Nurgak/Internet-of-Things-Power-Meter/Pictures/Misc/2015-12-24 13.48.35.jpg

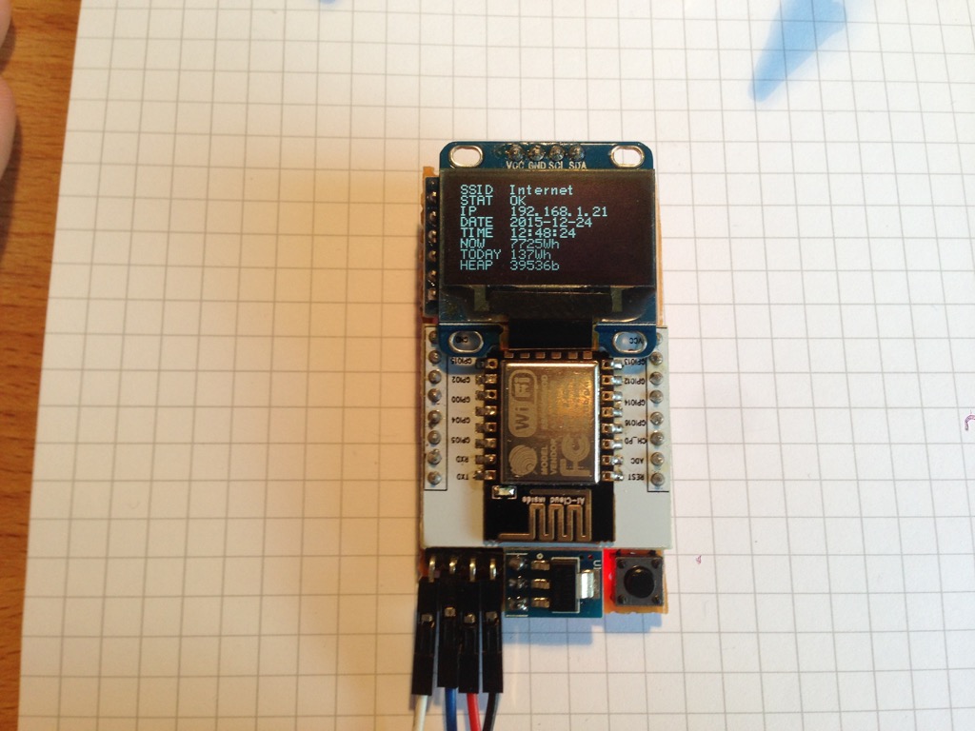
Pictures/Misc/2015-12-24 13.48.35.jpg
