Nurgak/Internet-of-Things-Power-Meter/Pictures/Misc/2015-12-24 13.49.23.jpg

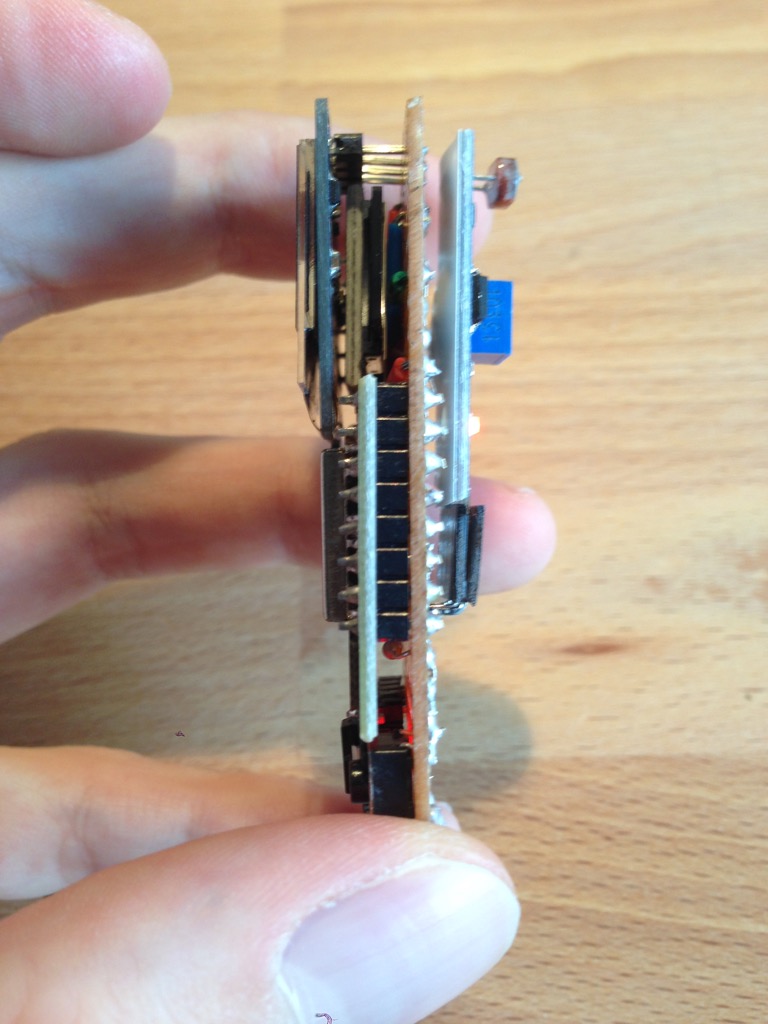
Pictures/Misc/2015-12-24 13.49.23.jpg
