Nurgak/Internet-of-Things-Power-Meter/Pictures/Misc/2015-12-24 13.50.25.jpg

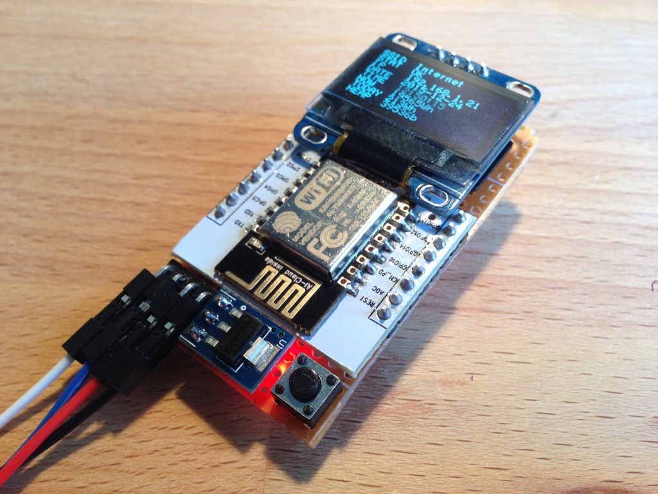
Pictures/Misc/2015-12-24 13.50.25.jpg
