Nurgak/Internet-of-Things-Power-Meter/Pictures/Misc/2016-03-25 19.55.58.jpg

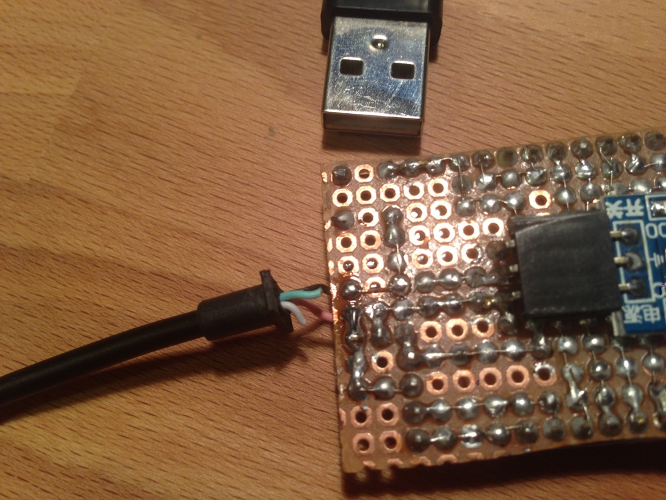
Pictures/Misc/2016-03-25 19.55.58.jpg
