Nurgak/Internet-of-Things-Power-Meter/Pictures/Misc/2016-03-27 12.49.37.jpg

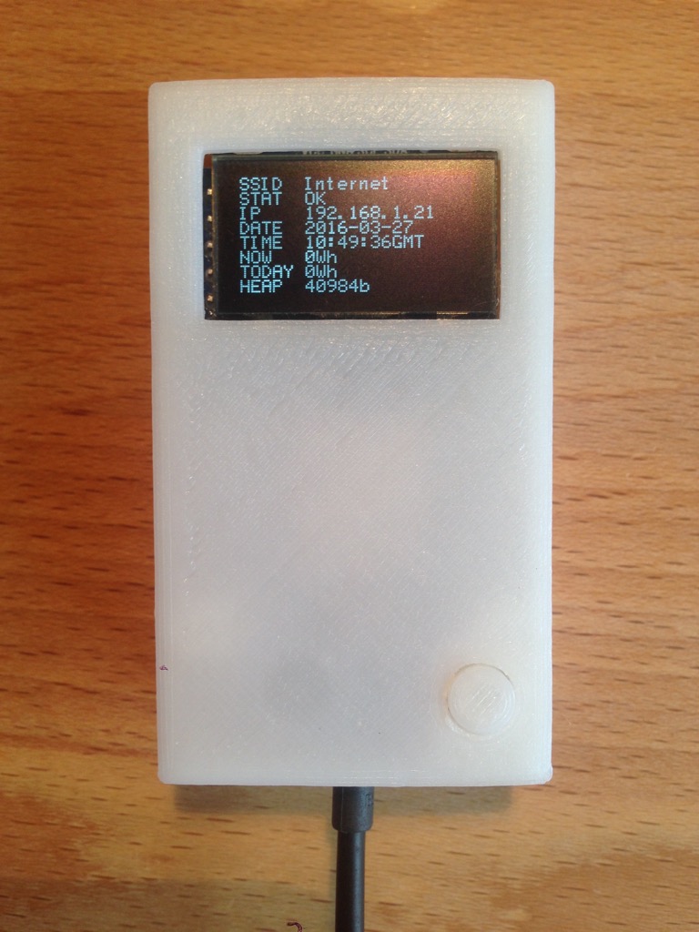
Pictures/Misc/2016-03-27 12.49.37.jpg
