Nurgak/Internet-of-Things-Power-Meter/Pictures/Misc/2016-03-27 12.50.36.jpg

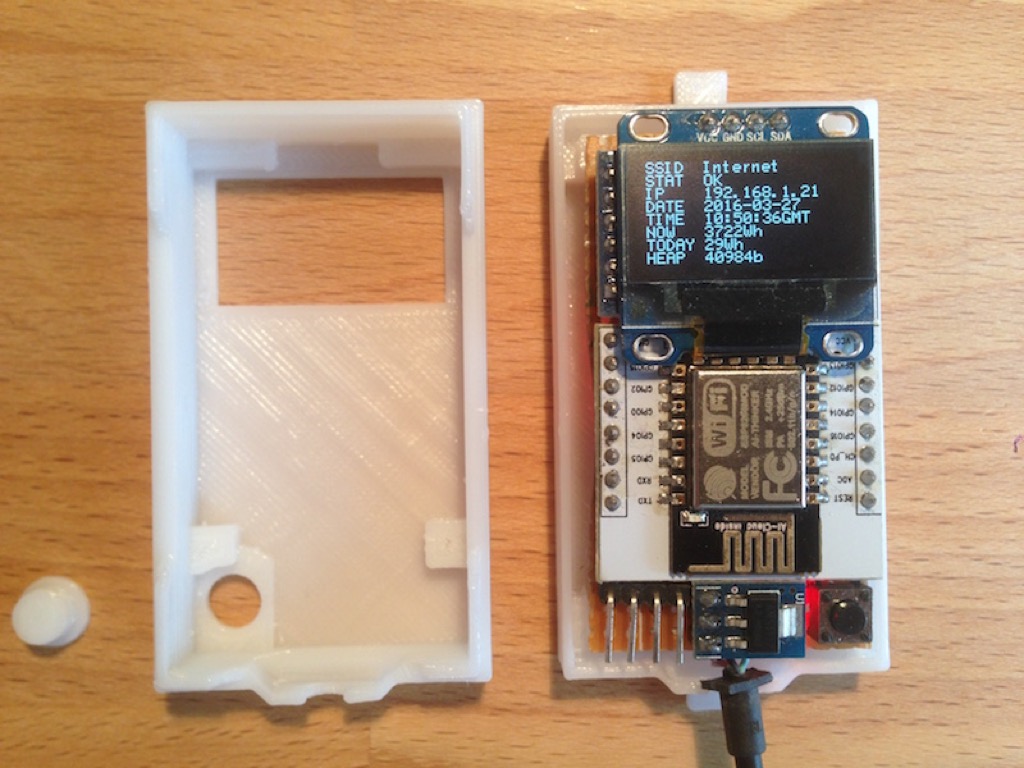
Pictures/Misc/2016-03-27 12.50.36.jpg
