Nurgak/Internet-of-Things-Power-Meter/Pictures/Misc/2016-03-27 13.48.42.jpg

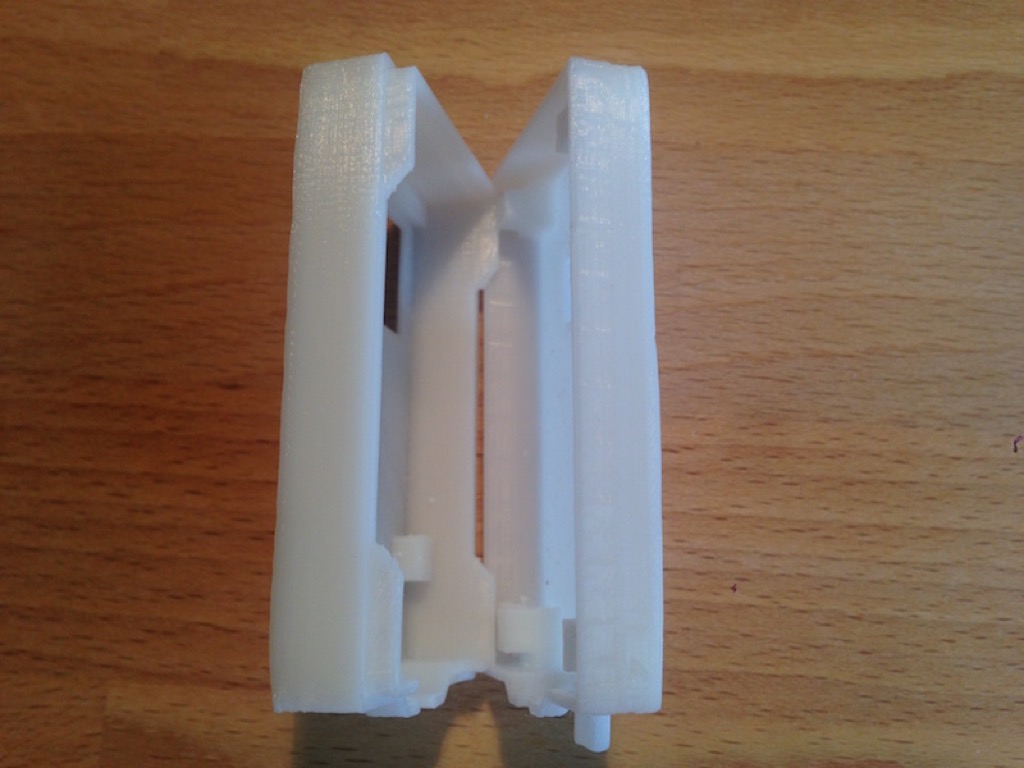
Pictures/Misc/2016-03-27 13.48.42.jpg
