Nurgak/Internet-of-Things-Power-Meter/Pictures/Misc/Graph.png

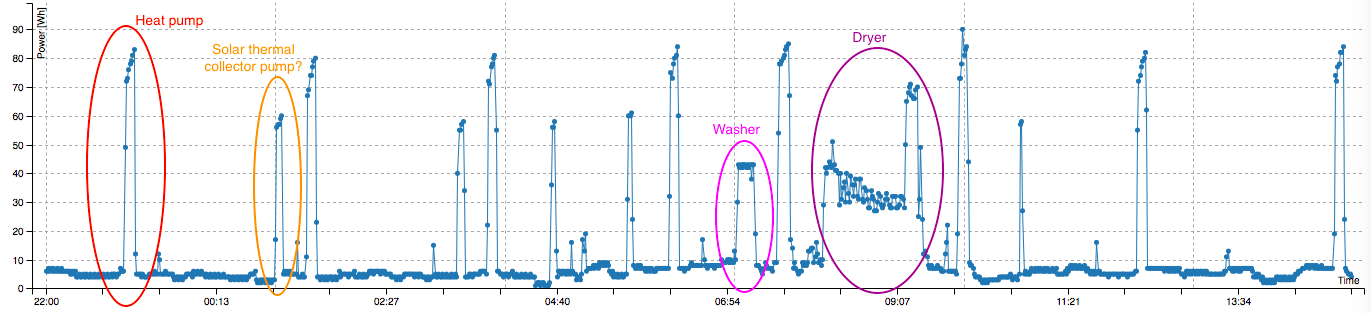
Pictures/Misc/Graph.png
