Nurgak/Internet-of-Things-Power-Meter/Pictures/Misc/IoT_Power_Meter_02.jpg

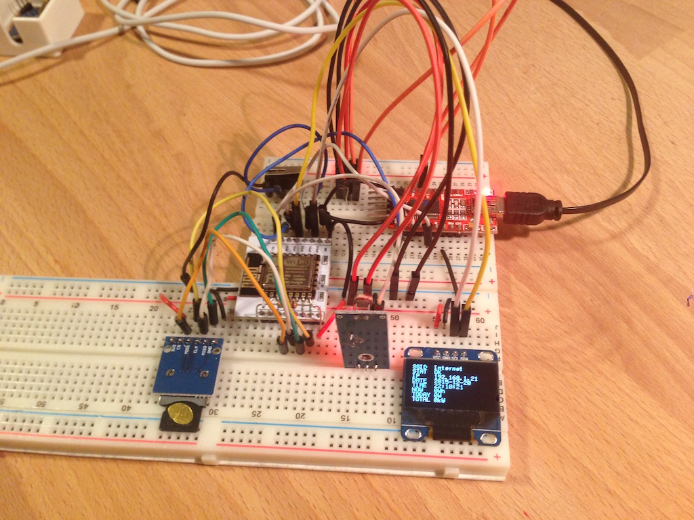
Pictures/Misc/IoT_Power_Meter_02.jpg
