Nurgak/Internet-of-Things-Power-Meter/Pictures/Misc/IPM.jpg

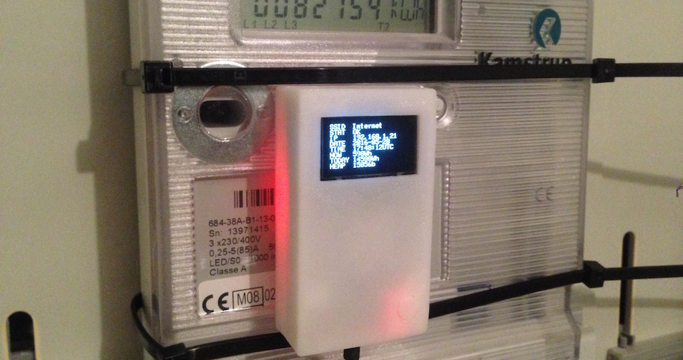
Pictures/Misc/IPM.jpg
