Nurgak/Internet-of-Things-Power-Meter/Pictures/Build/2015-12-22 19.23.27.jpg

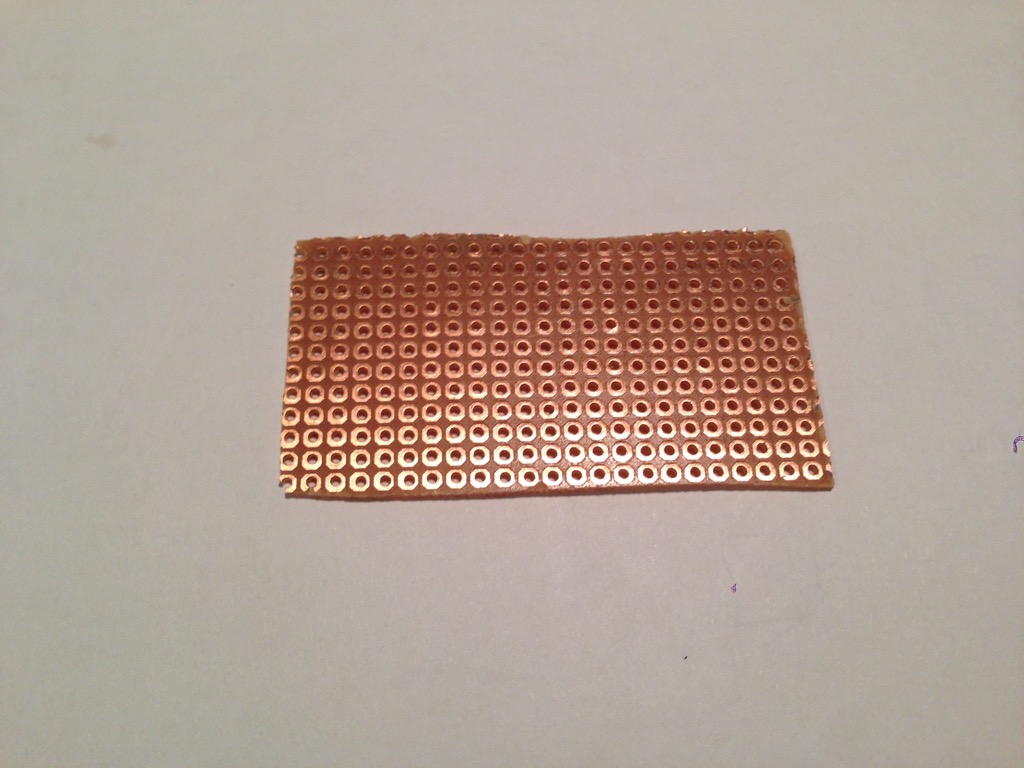
Pictures/Build/2015-12-22 19.23.27.jpg
