Nurgak/Internet-of-Things-Power-Meter/Pictures/Build/2015-12-23 22.53.20.jpg

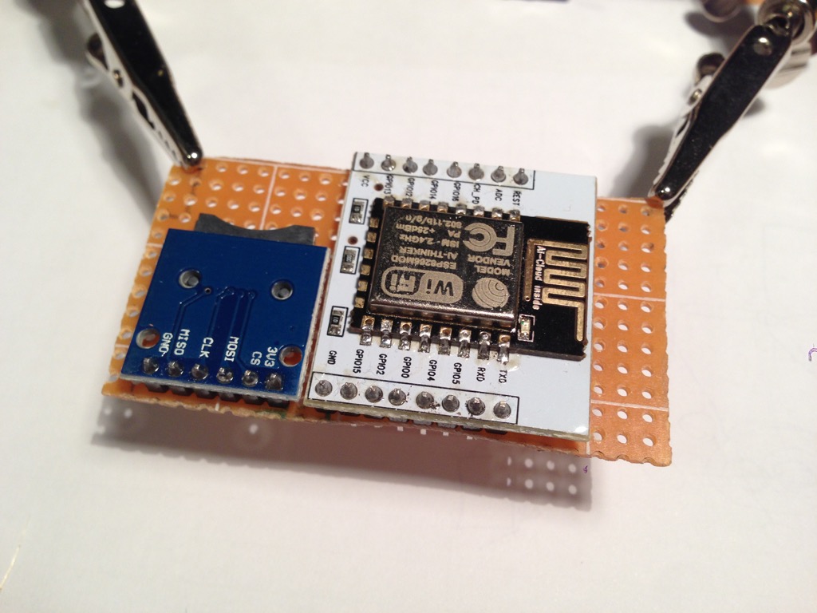
Pictures/Build/2015-12-23 22.53.20.jpg
