Nurgak/Internet-of-Things-Power-Meter/Pictures/Build/2015-12-23 22.57.33.jpg

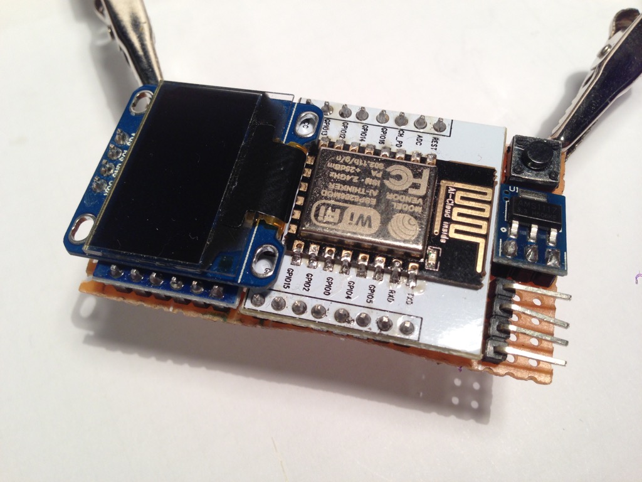
Pictures/Build/2015-12-23 22.57.33.jpg
