Nurgak/Internet-of-Things-Power-Meter/Pictures/Build/2016-04-08 20.18.40.jpg

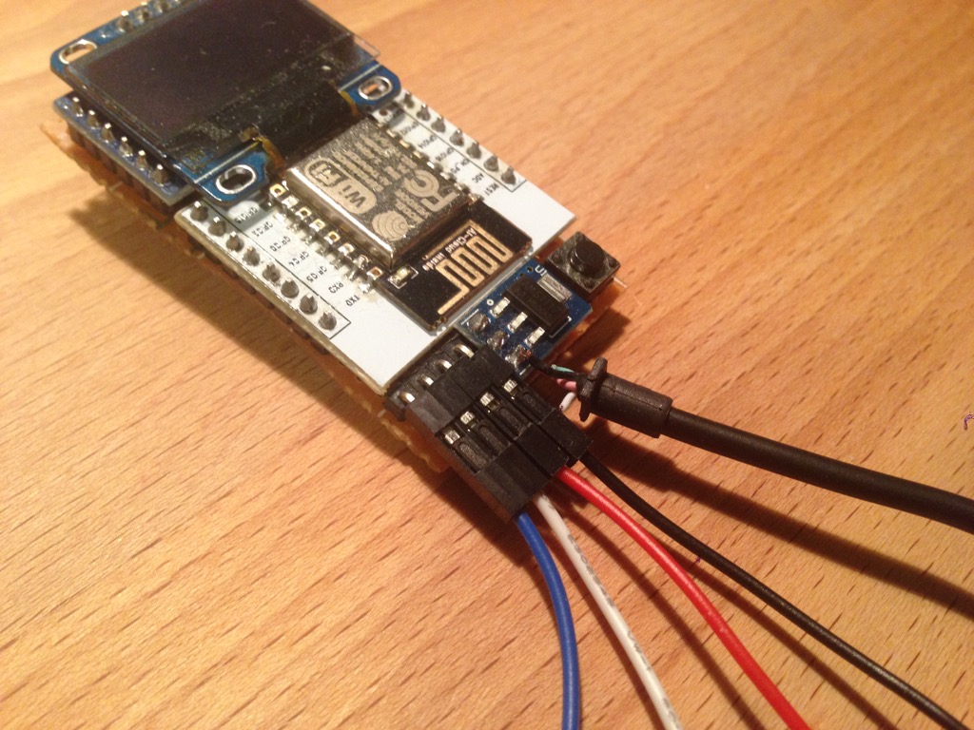
Pictures/Build/2016-04-08 20.18.40.jpg
