Nurgak/Internet-of-Things-Power-Meter/Pictures/Misc/IoT_Power_Meter_setup.png

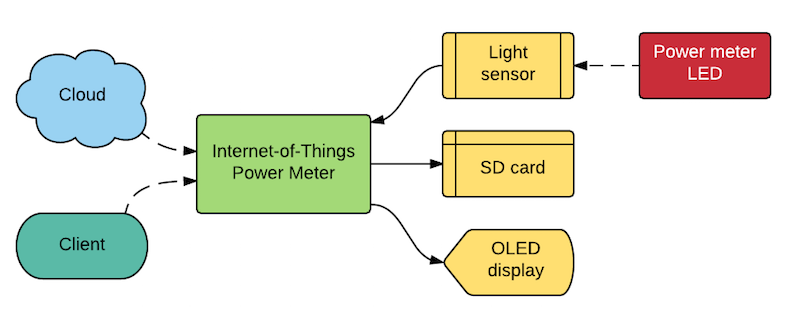
Pictures/Misc/IoT_Power_Meter_setup.png
