Nurgak/Internet-of-Things-Power-Meter/Software/IoTPowerMeterMQTT/ESP_SSD1306.cpp

/*
  IoTPowerMeter - Software for the IoTPowerMeter based on the ESP8266

  Copyright (c) 2016 Karl Kangur. All rights reserved.
  This file is part of IoTPowerMeter.

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
  You should have received a copy of the GNU General Public License
  along with IoTPowerMeter.  If not, see <http://www.gnu.org/licenses/>.
*/

/*
 * File:    ESP_SSD1306.cpp
 * Author:  Karl Kangur <karl.kangur@gmail.com>
 * Licnece: GPL
 * URL:     https://github.com/Nurgak/Internet-of-Things-Power-Meter
 */

#include <Wire.h>
#include "ESP_SSD1306.h"
#include "font.h"
#include "config.h"

void ICACHE_FLASH_ATTR ESP_SSD1306::begin(void)
{
  // SDA, SCL pin definitions in that order, can be any pin that can do interrupts
  Wire.begin(PIN_SDA, PIN_SCL);

  turnOff();

  // Reverse displayed data
  send(0xA1); // Bottom to top
  send(0xC8); // Right to left

  // Enable charge pump to
  send(SSD1306_CHARGEPUMP);
  send(0x14);

  // Clear the screen, turning screen on (inside reset()) is part of charge pump setting
  reset();
}

// Send commands to the display
void ICACHE_FLASH_ATTR ESP_SSD1306::send(unsigned char com)
{
  Wire.beginTransmission(address);
  Wire.write(0x80);
  Wire.write(com);
  Wire.endTransmission();
}

void ICACHE_FLASH_ATTR ESP_SSD1306::sendChar(unsigned char data)
{
  Wire.beginTransmission(address); // begin transmitting
  Wire.write(0x40);//data mode
  Wire.write(data);
  Wire.endTransmission();    // stop transmitting
}

// Prints a character on the display
void ICACHE_FLASH_ATTR ESP_SSD1306::sendCharXY(unsigned char data, unsigned char x, unsigned char y)
{
  setXY(x, y);
  Wire.beginTransmission(address);
  Wire.write(0x40);
  for(uint8_t i = 0; i < FONT_CHARACTER_WIDTH; i++)
  {
    // Skip the first 32 characters (0x20 = 32) as they are special and not defined
    Wire.write(pgm_read_byte(font[data - 0x20] + i));
  }
  Wire.endTransmission();
}

void ICACHE_FLASH_ATTR ESP_SSD1306::sendStrXY(const char * string, unsigned char x, unsigned char y)
{
  setXY(x, y);
  while(*string)
  {
    for(uint8_t i = 0; i < FONT_CHARACTER_WIDTH; i++)
    {
      // Skip the first 32 characters (0x20 = 32) as they are special and not defined
      sendChar(pgm_read_byte(font[*string - 0x20] + i));
    }
    *string++;
  }
}

// Set the cursor position
void ICACHE_FLASH_ATTR ESP_SSD1306::setXY(unsigned char row, unsigned char col)
{
  // Set page address
  send(0xb0 + row);
  // Transfer 2 nibbles for the column address
  // Set low column address, only send low nibble
  send(FONT_CHARACTER_WIDTH * col & 0x0f);
  // Set high column address, shift high nibble 4 bits to the right
  send(0x10 + ((FONT_CHARACTER_WIDTH * col >> 4) & 0x0f));
}

void ICACHE_FLASH_ATTR ESP_SSD1306::blank(void)
{
  clear();
  sendStrXY("STAT  ?", SCREEN_ROW_STAT,  SCREEN_TITLE_COLUMN);
  sendStrXY("IP    ?", SCREEN_ROW_IP,    SCREEN_TITLE_COLUMN);
  sendStrXY("DATE  ?", SCREEN_ROW_DATE,  SCREEN_TITLE_COLUMN);
  sendStrXY("TIME  ?", SCREEN_ROW_TIME,  SCREEN_TITLE_COLUMN);
  sendStrXY("NOW   ?", SCREEN_ROW_NOW,   SCREEN_TITLE_COLUMN);
  sendStrXY("TODAY ?", SCREEN_ROW_TODAY, SCREEN_TITLE_COLUMN);
  sendStrXY("HEAP  ?", SCREEN_ROW_HEAP,  SCREEN_TITLE_COLUMN);
}

// Clears the display by sendind 0 to all the screen map.
void ICACHE_FLASH_ATTR ESP_SSD1306::clear(void)
{
  uint8_t k;
  // For every line
  for(k = 0; k < SSD1306_SETTINGS_LINES; k++)
  {
    clear(k, 0);
  }
}

// Clear the line y starting from the position x
void ICACHE_FLASH_ATTR ESP_SSD1306::clear(unsigned char row, unsigned char col)
{
  setXY(row, col);
  // For every column
  for(uint8_t i = FONT_CHARACTER_WIDTH * col; i < SSD1306_SETTINGS_PIXELS; i++)
  {
    // A column of a line is 8 bits
    sendChar(0x0);
  }
}

void ICACHE_FLASH_ATTR ESP_SSD1306::reset(void)
{
  turnOff();
  clear();
  turnOn();
}

// Turns display on.
void ICACHE_FLASH_ATTR ESP_SSD1306::turnOn(void)
{
  send(SSD1306_DISPLAYON);
}

// Turns display off.
void ICACHE_FLASH_ATTR ESP_SSD1306::turnOff(void)
{
  send(SSD1306_DISPLAYOFF);
}
