Nurgak/Internet-of-Things-Power-Meter/Software/IoTPowerMeter/push.cpp

/*
  IoTPowerMeter - Software for the IoTPowerMeter based on the ESP8266

  Copyright (c) 2016 Karl Kangur. All rights reserved.
  This file is part of IoTPowerMeter.

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
*/

/*
 * File:    push.cpp
 * Author:  Karl Kangur <karl.kangur@gmail.com>
 * Licnece: GPL
 * URL:     https://github.com/Nurgak/Internet-of-Things-Power-Meter
 */

#include <WiFiClientSecure.h>
#include <TimeLib.h>

#include "config.h"
#include "push.h"

GoogleSpreadsheets::GoogleSpreadsheets(const char * _script)
{
  // Define the Google Spreadsheets host
  host = "script.google.com";
  script = _script;
}

bool GoogleSpreadsheets::submit(time_t time, uint16_t power)
{
  DEBUGV("Submitting data to Google Spreadsheets\n");
  
  // Connect to Google Spreadsheets
  if (!client.connect(host, 443))
  {
    DEBUGV("Connection failed\n");
    return false;
  }

  // This has been commented out as Google changes its SHA1 certificate depending on the server which is used
  // No certificate veritication is done as the upload would fail from time to time
  // Reference: http://www.esp8266.com/viewtopic.php?f=32&t=8981#p44253
  /*// Check that the fingerprint matches
  if(!client.verify(fingerprint, host))
  {
    DEBUGV("Certificate not valid\n");
    return false;
  }*/

  // Construct the GET request
  String url = String(script) + "?time=" + time + "&power=" + power + "&token=" + googleSpreadSheetsToken;

  client.print(String("GET ") + url + " HTTP/1.1\r\nHost: " + host + "\r\nConnection: close\r\n\r\n");
  
  // At this point we might as well assume the request was successful,
  // however for debugging one can view the server response by uncommending the following block:
  /*while(client.connected())
  {
    String line = client.readStringUntil('\n');
    DEBUGV(line);
  }*/

  DEBUGV("Sumission succeeded\n");
  return true;
}
